get-adr/PixelStatus/src/Icons.h

#pragma once
#include <Arduino.h>

// Icon-Assets fuer Web-UI-Favicon/PWA (WebPortal.cpp) und generiert aus
// PixelStatus Logo.png (August 2026): quadratisch gepolstert auf
// 1024x1024 (transparenter Hintergrund erhalten), dann pro Zielgroesse mit
// Pillow (LANCZOS) herunterskaliert und mit pngquant --nofs (kein Dithering --
// bei diesem flachen 3-Farb-Motiv kleiner UND sauberer als mit Dithering)
// nachkomprimiert. Bei einem neuen Logo einfach denselben Weg wiederholen und
// diese Datei komplett ersetzen -- kein Teil davon wird von Hand gepflegt.
// FAVICON_ICO: 16/32/48px gebuendelt (Windows-Taskleiste/Legacy-Browser).
// FAVICON_PNG: 32px (<link rel="icon" type="image/png">, scharfe Browser-Tabs).
// APPLE_TOUCH_ICON_PNG: 180px (iOS "Zum Home-Bildschirm").
// ICON_192_PNG/ICON_512_PNG: PWA-Manifest-Icons (siehe /manifest.json).

static const uint8_t FAVICON_ICO[] PROGMEM = {
0x00,0x00,0x01,0x00,0x01,0x00,0x10,0x10,0x00,0x00,0x00,0x00,0x20,0x00,0x2b,0x02,0x00,0x00,0x16,0x00,
0x00,0x00,0x89,0x50,0x4e,0x47,0x0d,0x0a,0x1a,0x0a,0x00,0x00,0x00,0x0d,0x49,0x48,0x44,0x52,0x00,0x00,
0x00,0x10,0x00,0x00,0x00,0x10,0x08,0x06,0x00,0x00,0x00,0x1f,0xf3,0xff,0x61,0x00,0x00,0x01,0xf2,0x49,
0x44,0x41,0x54,0x78,0x9c,0xa5,0x92,0xcd,0x4e,0x53,0x51,0x14,0x85,0xbf,0xb5,0x6f,0x69,0x81,0x1a,0x28,
0x05,0x8d,0xa1,0x18,0xfc,0xc1,0x98,0x38,0x73,0xe2,0x5b,0xf8,0x00,0xfa,0x88,0x3e,0x06,0x13,0xdf,0xc1,
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
0x0c,0x06,0x83,0xc1,0x60,0x30,0x18,0x0c,0x06,0x83,0xc1,0x60,0x30,0x18,0x0c,0x06,0x83,0xc1,0x60,0x30,
0x18,0x0c,0x06,0x83,0xc1,0x60,0xfe,0x4f,0x19,0xbe,0xe1,0x96,0x3a,0xf2,0x73,0x54,0xe4,0xed,0x64,0x98,
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
};
static const size_t ICON_512_PNG_LEN = 52604;
